adriabrucortes/DIJOUS_4_PORTES/DIJOUS_4_PORTES-master/PCB/motors.kicad_sch

## KiCad design DIJOUS_4_PORTES-master/PCB/motors.kicad_sch (2024-04-10)

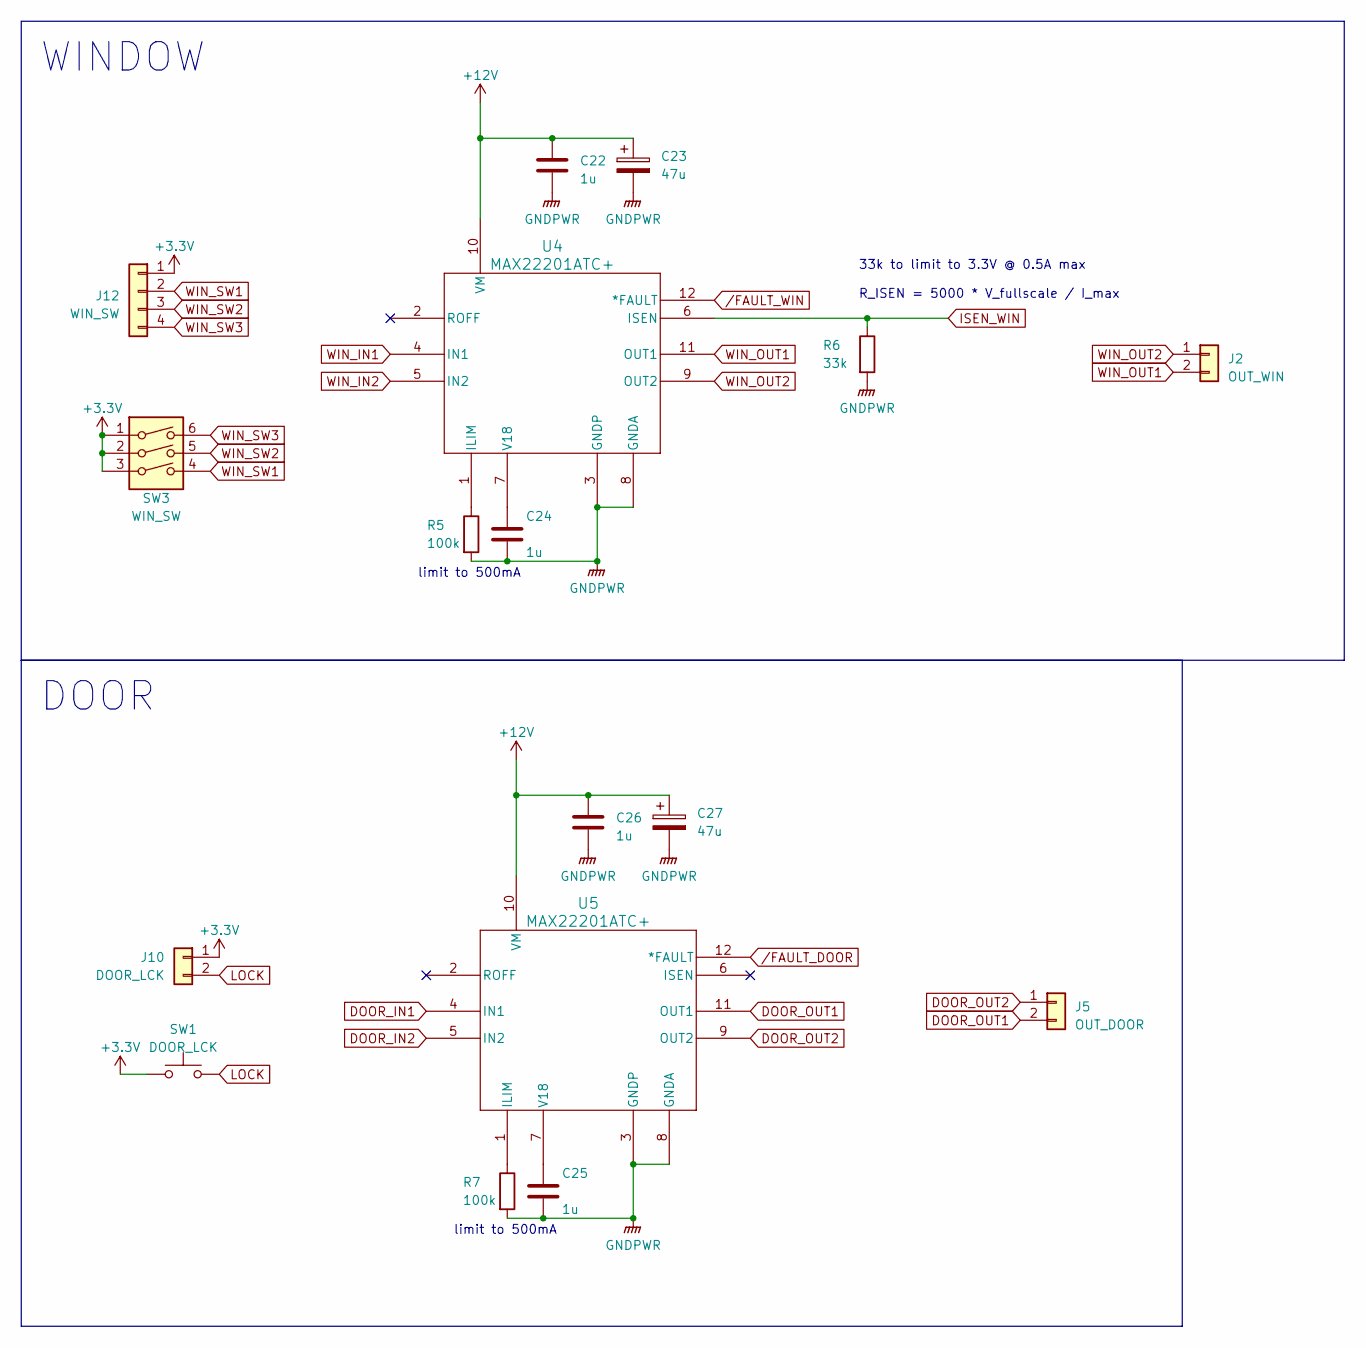
[picture p20: schematic motors.kicad_sch]

Parts:
C22, C24, C25, C26: 1u; C_0805_2012Metric
C23, C27: 47u; CP_Radial_D5.0mm_P2.00mm
J2: OUT_WIN; TerminalBlock_MetzConnect_Type011_RT05502HBWC_1x02_P5.00mm_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
J5: OUT_DOOR; TerminalBlock_MetzConnect_Type011_RT05502HBWC_1x02_P5.00mm_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
J10: DOOR_LCK; TerminalBlock_MetzConnect_Type011_RT05502HBWC_1x02_P5.00mm_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
J12: WIN_SW; TerminalBlock_MetzConnect_Type011_RT05504HBWC_1x04_P5.00mm_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
R5, R7: 100k; R_0805_2012Metric
R6: 33k; R_0805_2012Metric
SW1: DOOR_LCK; SW_CW_GPTS203211B
SW3: WIN_SW; SW_DIP_SPSTx03_Slide_6.7x9.18mm_W8.61mm_P2.54mm_LowProfile
U4, U5: MAX22201ATC+; MAX22201ATC_

Connections:
+3.3V: J10.1, J12.1, SW1.1, SW3.1, SW3.2, SW3.3
+12V: C22.1, C23.1, C26.1, C27.1, U4.10 (VM), U5.10 (VM)
DOOR_IN1: U5.4 (IN1)
DOOR_IN2: U5.5 (IN2)
DOOR_OUT1: J5.2, U5.11 (OUT1)
DOOR_OUT2: J5.1, U5.9 (OUT2)
GNDPWR: C22.2, C23.2, C24.2, C25.2, C26.2, C27.2, R5.2, R6.2, R7.2, U4.3 (GNDP), U4.8 (GNDA), U5.3 (GNDP), U5.8 (GNDA)
ISEN_WIN: R6.1, U4.6 (ISEN)
LOCK: J10.2, SW1.2
unnamed: C24.1, U4.7 (V18)
unnamed: C25.1, U5.7 (V18)
unnamed: R5.1, U4.1 (ILIM)
unnamed: R7.1, U5.1 (ILIM)
WIN_IN1: U4.4 (IN1)
WIN_IN2: U4.5 (IN2)
WIN_OUT1: J2.2, U4.11 (OUT1)
WIN_OUT2: J2.1, U4.9 (OUT2)
WIN_SW1: J12.2, SW3.4
WIN_SW2: J12.3, SW3.5
WIN_SW3: J12.4, SW3.6
/FAULT_DOOR: U5.12 (*FAULT)
/FAULT_WIN: U4.12 (*FAULT)

Notes on the sheet:
DOOR
WINDOW
33k to limit to 3.3V @ 0.5A max R_ISEN = 5000 * V_fullscale / I_max
limit to 500mA
